Tyger375/Sampler/esp32_rust/components/main_rust/src/utils.rs

use std::ptr;
use esp_idf_svc::sys::uxTaskGetStackHighWaterMark;

pub const MAX_MIDI_NOTE: u8 = 127;
pub const MAX_MIDI_CHANNELS: u8 = 16;

const NOTE_NAMES: [&str; 12] = ["C", "C#", "D", "D#", "E", "F", "F#", "G", "G#", "A", "A#", "B"];

pub fn int_to_note(note: i32) -> String {
    if note < 0 || note > MAX_MIDI_NOTE as i32 {
        return String::from("---")
    }

    let octave = (note / 12) - 1;
    let name_index = (note % 12) as usize;

    format!("{}{}", NOTE_NAMES[name_index], octave)
}

extern "C" {
    fn esp_delay_us(micros: u32);
    fn log_timestamp() -> u32;
    fn timer_get_time() -> u32;
}

pub fn delay_us(micros: u32) {
    unsafe {
        esp_delay_us(micros);
    }
}

pub fn timestamp() -> u32 {
    unsafe { log_timestamp() }
}

pub fn get_time() -> u32 {
    unsafe { timer_get_time() }
}

pub fn log_main_stack(label: &str) {
    // Get the minimum free stack space ever reached by the current task
    // Returns value in "words" (4 bytes each)
    let stack_words = unsafe { uxTaskGetStackHighWaterMark(ptr::null_mut()) };
    let stack_bytes = stack_words * 4;

    log::info!("--- Stack Report [{}] ---", label);
    log::info!("Min free stack: {} bytes", stack_bytes);
}

pub fn pad_to_seq(channel: u8) -> u8 {
    (channel / 2) + (channel % 2) * 4
}

pub fn seq_to_pad(seq: u8) -> u8 {
    (seq % 4) * 2 + (seq / 4)
}

#[derive(Copy, Clone, Debug, Default)]
pub struct CustomGraphicsEvent {
    data: u32
}

impl From<u32> for CustomGraphicsEvent {
    fn from(value: u32) -> Self {
        CustomGraphicsEvent {
            data: value
        }
    }
}

impl From<CustomGraphicsEvent> for u32 {
    fn from(value: CustomGraphicsEvent) -> Self {
        value.data
    }
}

impl CustomGraphicsEvent {
    const CHANNEL_MASK: u32 = 0b111;
    const LONG_CLICK_BIT: u32 = 1 << 3;
    const SHORTCUT_BIT: u32 = 1 << 4;

    pub fn new() -> Self {
        Self::default()
    }

    pub fn with_channel(mut self, channel: u8) -> Self {
        self.data = (self.data & !Self::CHANNEL_MASK) | (channel as u32 & 0b111);
        self
    }

    pub fn set_long_click(&mut self, is_long: bool) {
        if is_long {
            self.data |= Self::LONG_CLICK_BIT;
        } else {
            self.data &= !Self::LONG_CLICK_BIT;
        }
    }

    pub fn set_shortcut(&mut self, is_shortcut: bool) {
        if is_shortcut {
            self.data |= Self::SHORTCUT_BIT;
        } else {
            self.data &= !Self::LONG_CLICK_BIT;
        }
    }

    pub fn get_channel(&self) -> u8 {
        (self.data & Self::CHANNEL_MASK) as u8
    }

    pub fn is_long_click(&self) -> bool {
        (self.data & Self::LONG_CLICK_BIT) != 0
    }

    pub fn is_shortcut(&self) -> bool {
        (self.data & Self::SHORTCUT_BIT) != 0
    }
}
